wilco2009/ZX81KBD-PLUS/Arduino/zx81kbdplusV0_8_ESP2866/GLOBAL.h

#define CONFIG_VER 1

#if defined (__AVR__)
  #warning compiling for AVR
  const int DataPin = A2;
  const int IRQpin =  3;
  #define CLK   A3 
  #define NRST  A6
  #define C0    A1
  #define C1    2
  #define C2    4
  #define C3    5
  #define C4    6
// #elif defined (UNOR4)
//   #warning compiling for UNOR4
//   const int DataPin = A2;
//   const int IRQpin =  3;
//   #define CLK   A3 
//   #define NRST  A6
//   #define C0    A1
//   #define C1    2
//   #define C2    4
//   #define C3    5
//   #define C4    6
#elif defined (__XTENSA__) //ESP32S3
  #warning compiling for ESP32S3
  #define EEPROM_SIZE 100
  const int DataPin = 39;
  const int IRQpin =  40;
  #define CLK   6 
  #define NRST  7
  #define C0    1
  #define C1    2
  #define C2    3
  #define C3    4
  #define C4    5
#else
#error Compiling for unsupported target.
#endif

#define UP    0
#define DOWN  1
#define LEFT  2
#define RIGHT 3
#define BUTB  4
#define TRIG  5
#define BUTA  6

#define JUP     (value & 1)==0
#define JDOWN   (value & 2)==0
#define JLEFT   (value & 4)==0
#define JRIGHT  (value & 8)==0
#define JBUTB   (value & 16)==0
#define JTRIGER (value & 32)==0
#define JBUTA   (value & 64)==0
#define CONFIG  (value & 128)==0
#define BLINK (millis() % 64) <32

#define PREV_JUP     (prev_value & 1)==0
#define PREV_JDOWN   (prev_value & 2)==0
#define PREV_JLEFT   (prev_value & 4)==0
#define PREV_JRIGHT  (prev_value & 8)==0
#define PREV_JBUTB   (prev_value & 16)==0
#define PREV_JTRIGER (prev_value & 32)==0
#define PREV_JBUTA   (prev_value & 64)==0

uint8_t config_ver;
uint8_t currentKeyboard = 0;
boolean USB_connected = false;


uint8_t joyKeys[] = {
  10,   // UP = Q
  5,    // DOWN = A
  26,   // LEFT = O
  25,   // RIGHT = P
  35,   // BUTB = SPACE
  20,   // TRIG = 
  30    // BUTA = ENTER
};
char buffer[10];


void saveConfig(){
  #if defined (__XTENSA__)
    uint8_t ver;
    boolean modified = false;
    EEPROM.get(0, ver);
    if (ver!=CONFIG_VER) {
      EEPROM.write(0,CONFIG_VER);
      modified = true;
    }
    for (int i=0; i<7; i++){
      uint8_t key;
      EEPROM.get(i+2, key);
      if (key!=joyKeys[i]){
        EEPROM.write(i+2,joyKeys[i]);
        modified = true;
      }
    }
    if (modified) EEPROM.commit();
  #else
    EEPROM.update(0,CONFIG_VER);
    EEPROM.update(1,currentKeyboard);
    for (int i=0; i<7; i++){
      EEPROM.update(i+2,joyKeys[i]);
    }
  #endif
}


uint8_t C[5]={C0,C1,C2,C3,C4};
uint8_t rows[8]={0xff,0xff,0xff,0xff,0xff,0xff,0xff,0xff};
//char SJOY[10] ="QAOP0>          ";
    // if (JUP)      SJOY[0]='U'; else SJOY[0]=' ';
    // if (JDOWN)    SJOY[1]='D'; else SJOY[1]=' ';
    // if (JLEFT)    SJOY[2]='L'; else SJOY[2]=' ';
    // if (JRIGHT)   SJOY[3]='R'; else SJOY[3]=' ';
    // if (JBUTA)    SJOY[4]='A'; else SJOY[4]=' ';
    // if (JBUTB)    SJOY[5]='B'; else SJOY[5]=' ';
    // if (JTRIGER)  SJOY[6]='T'; else SJOY[6]=' ';
    // if (CONFIG)   SJOY[7]='C'; else SJOY[7]=' ';

uint8_t value = 255;
uint8_t prev_value = 255;
//U8G2_SSD1306_128X32_UNIVISION_1_HW_I2C u8g2(U8G2_R2); //, /* clock=*/ 21, /* data=*/ 20, /* reset=*/ U8X8_PIN_NONE);   // Adafruit Feather M0 Basic Proto + FeatherWing OLED
//U8G2_SSD1306_128X32_UNIVISION_F_HW_I2C u8g2(U8G2_R2, /* reset=*/ U8X8_PIN_NONE, /* clock=*/ SCL, /* data=*/ SDA);   // pin remapping with ESP8266 HW I2C
U8G2_SSD1306_128X32_UNIVISION_1_HW_I2C u8g2(U8G2_R2, /* reset=*/ U8X8_PIN_NONE, /* clock=*/SCL, /* data=*/ SDA);   // pin remapping with ESP8266 HW I2C
const int pcfAddress = 0x20;
short channel = 1;

void u8g2_drawStringP(uint8_t x, uint8_t y, const char * progmem_ptr) {
  u8g2.setCursor(x, y);
  u8g2.print((const __FlashStringHelper *)progmem_ptr);  // use arduino progmem print
}

const char keys[8][5]={
  {'s','Z','X','C','V'},
  {'A','S','D','F','G'},
  {'Q','W','E','R','T'},
  {'1','2','3','4','5'},

  {'0','9','8','7','6'},
  {'P','O','I','U','Y'},
  {'>','L','K','J','H'},
  {'-','.','M','N','B'}
};

uint8_t ch_w = 8;
uint8_t ch_h = 8;

char getCharKey(uint8_t key){
  uint8_t row = (key & 0b00111111) / 5;
  uint8_t column = (key & 0b00111111) % 5;
  return keys[row][column];
}

/* prints hex numbers with leading zeroes */
void print_hex(int v, int num_places) {
        int mask = 0, n, num_nibbles, digit;

        for(n = 1; n <= num_places; n++) {
                mask = (mask << 1) | 0x0001;
        }
        v = v & mask; // truncate v to specified number of places

        num_nibbles = num_places / 4;
        if((num_places % 4) != 0) {
                ++num_nibbles;
        }
        do {
                digit = ((v >> (num_nibbles - 1) * 4)) & 0x0f;
                Serial.print(digit, HEX);
        } while(--num_nibbles);
}
