wilco2009/ZX81KBD-PLUS/Arduino/zx81kbdplusV0_8_ESP2866/LOGO.h

#define ZXKBDPLUS_width 128
#define ZXKBDPLUS_height 32
const static unsigned char PROGMEM ZXKBDPLUS_bits[] = {
   0x00, 0x00, 0x00, 0x00, 0x00, 0x00, 0x00, 0x00, 0x00, 0x00, 0x00, 0x00,
   0x00, 0x00, 0x00, 0x00, 0x00, 0x00, 0x00, 0x00, 0x00, 0x00, 0x00, 0x00,
   0x00, 0x00, 0x00, 0x00, 0x00, 0x00, 0x00, 0x00, 0x00, 0x00, 0xf0, 0xff,
   0xcf, 0x0f, 0xf8, 0x01, 0x00, 0x00, 0x00, 0x00, 0x00, 0x00, 0x00, 0x00,
   0x00, 0x00, 0xf0, 0xff, 0x8f, 0x0f, 0xf8, 0x00, 0x00, 0x00, 0x00, 0x00,
   0x00, 0x00, 0x00, 0x00, 0x00, 0x00, 0xf0, 0xff, 0x8f, 0x1f, 0x7c, 0x00,
   0x00, 0x00, 0x00, 0x00, 0x00, 0x00, 0x00, 0x00, 0x00, 0x00, 0xf0, 0xff,
   0x07, 0x1f, 0x7c, 0x00, 0x00, 0x00, 0x00, 0x00, 0x00, 0x00, 0x00, 0x00,
   0x00, 0x00, 0x00, 0xe0, 0x07, 0x3f, 0x3e, 0x00, 0x00, 0x00, 0x00, 0x00,
   0x00, 0x00, 0x00, 0x00, 0x00, 0x00, 0x00, 0xe0, 0x03, 0x3e, 0x3e, 0x00,
   0x00, 0x00, 0x00, 0x00, 0x00, 0x00, 0x00, 0x00, 0x00, 0x00, 0x00, 0xf0,
   0x01, 0x7e, 0x1f, 0x00, 0x00, 0x00, 0x00, 0x00, 0x00, 0x00, 0x00, 0x00,
   0x00, 0x00, 0x00, 0xf8, 0x01, 0x7c, 0x0f, 0x00, 0x00, 0x00, 0x00, 0x00,
   0x00, 0x00, 0x00, 0x00, 0x00, 0x00, 0x00, 0xf8, 0x00, 0xf8, 0x0f, 0x00,
   0x00, 0x00, 0x00, 0x00, 0x00, 0x00, 0x00, 0x00, 0x00, 0x00, 0x00, 0x7c,
   0x00, 0xf8, 0x07, 0x00, 0x00, 0x00, 0x00, 0x00, 0x00, 0x00, 0x00, 0x00,
   0x00, 0x00, 0x00, 0x7e, 0x00, 0xf0, 0x07, 0x80, 0xe3, 0xfd, 0xe1, 0x1f,
   0x00, 0x00, 0x00, 0x00, 0x00, 0x00, 0x00, 0x3f, 0x00, 0xf0, 0x07, 0x80,
   0xe3, 0xfc, 0xe7, 0x3f, 0x00, 0x00, 0x00, 0x00, 0x00, 0x00, 0x00, 0x1f,
   0x00, 0xf8, 0x07, 0x80, 0x73, 0x1c, 0xe7, 0x78, 0x00, 0x00, 0x00, 0x00,
   0x00, 0x00, 0x80, 0x1f, 0x00, 0xfc, 0x0f, 0x80, 0x3b, 0x1c, 0xe7, 0xf0,
   0xc0, 0x00, 0x00, 0x00, 0x00, 0x00, 0xc0, 0x0f, 0x00, 0xfc, 0x1f, 0x80,
   0x3b, 0x1c, 0xe3, 0xe0, 0xc0, 0x00, 0x00, 0x00, 0x00, 0x00, 0xc0, 0x07,
   0x00, 0x3e, 0x1f, 0x80, 0x1f, 0xfc, 0xe1, 0xe0, 0xc0, 0x00, 0x00, 0x00,
   0x00, 0x00, 0xe0, 0x03, 0x00, 0x3f, 0x3f, 0x80, 0x1f, 0xfc, 0xe3, 0xe0,
   0xf8, 0x07, 0x00, 0x00, 0x00, 0x00, 0xf0, 0x03, 0x00, 0x1f, 0x3e, 0x80,
   0x3b, 0x1c, 0xe7, 0xe0, 0xf8, 0x07, 0x00, 0x00, 0x00, 0x00, 0xf8, 0xff,
   0x8f, 0x1f, 0x7e, 0x80, 0x7b, 0x1c, 0xe7, 0x70, 0xc0, 0x00, 0x00, 0x00,
   0x00, 0x00, 0xf8, 0xff, 0x8f, 0x0f, 0xfc, 0x80, 0x73, 0x1c, 0xe7, 0x78,
   0xc0, 0x00, 0x00, 0x00, 0x00, 0x00, 0xf8, 0xff, 0xcf, 0x0f, 0xfc, 0x80,
   0xe3, 0xfc, 0xe3, 0x3f, 0xc0, 0x00, 0x00, 0x00, 0x00, 0x00, 0xf8, 0xff,
   0xef, 0x07, 0xf8, 0x81, 0xe3, 0xfd, 0xe1, 0x0f, 0x00, 0x00, 0x00, 0x00,
   0x00, 0x00, 0x00, 0x00, 0x00, 0x00, 0x00, 0x00, 0x00, 0x00, 0x00, 0x00,
   0x00, 0x00, 0x00, 0x00, 0xc0, 0xff, 0xff, 0xff, 0xff, 0xff, 0xff, 0xff,
   0xff, 0xff, 0xff, 0xff, 0xff, 0xff, 0xff, 0x03, 0x00, 0x00, 0x00, 0x00,
   0x00, 0x00, 0x00, 0x00, 0x00, 0x00, 0x00, 0x00, 0x00, 0x00, 0x00, 0x00,
   0x00, 0xf8, 0xff, 0xff, 0xff, 0xff, 0xff, 0xff, 0xff, 0xff, 0xff, 0xff,
   0xff, 0xff, 0x3f, 0x00, 0x00, 0x00, 0x00, 0x00, 0x00, 0x00, 0x00, 0x00,
   0x00, 0x00, 0x00, 0x00, 0x00, 0x00, 0x00, 0x00, 0x00, 0x00, 0xff, 0xff,
   0xff, 0xff, 0xff, 0xff, 0xff, 0xff, 0xff, 0xff, 0xff, 0xff, 0x00, 0x00,
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
